QuickTrollHosted/LoKy/LoKy_Documentation/Pin_Out/F_header.jpg

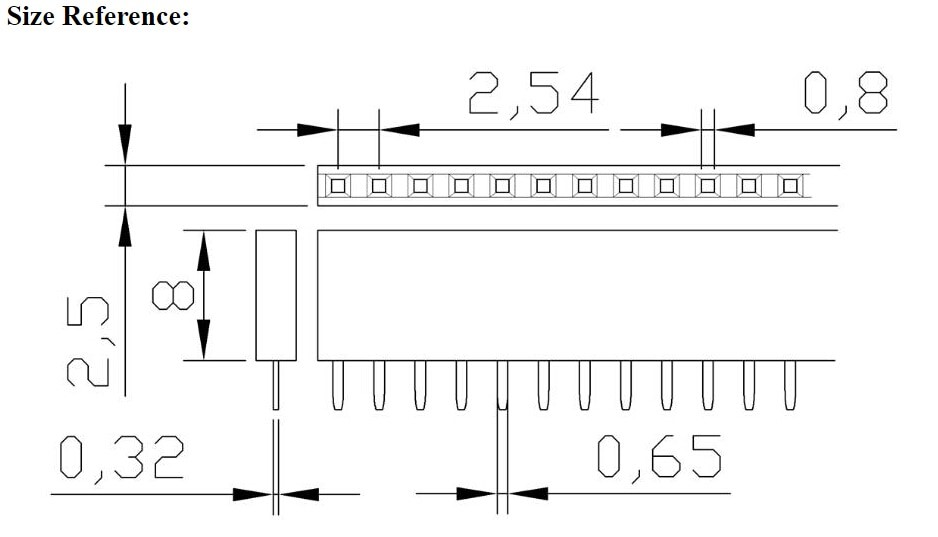
LoKy_Documentation/Pin_Out/F_header.jpg
