QuickTrollHosted/LoKy/LoKy_Documentation/Pin_Out/MCP1702.PNG

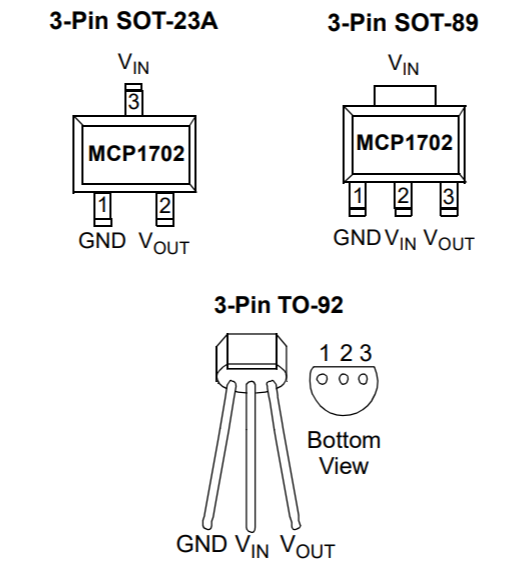
LoKy_Documentation/Pin_Out/MCP1702.PNG
