QuickTrollHosted/LoKy/LoKy_Documentation/Pin_Out/RFM95.png

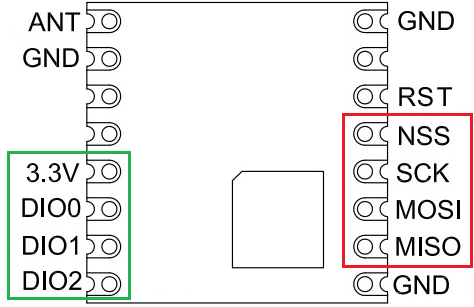
LoKy_Documentation/Pin_Out/RFM95.png
