QuickTrollHosted/LoKy/LoKy_Documentation/Pin_Out/Uno+ATMEGA328p_PinOut.jpg

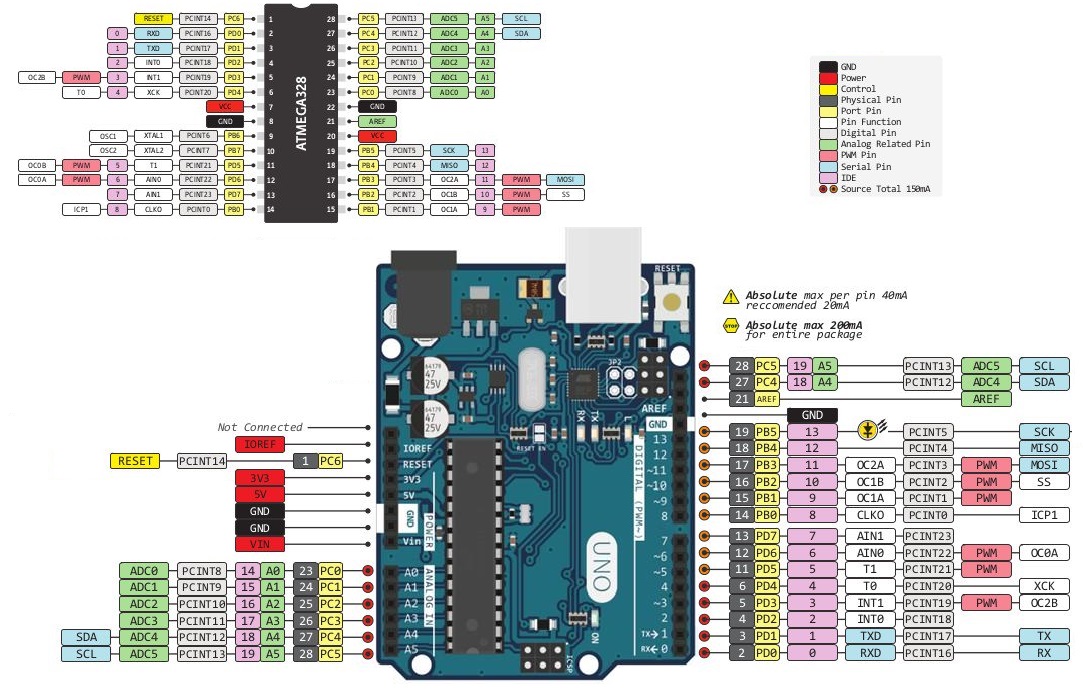
LoKy_Documentation/Pin_Out/Uno+ATMEGA328p_PinOut.jpg
